jarmitage/Stenophone/teensyduino/stenophone/stenophone.h

#define TOTAL_CHANNELS 24
#define USED_CHANNELS 22

//============================================
//  Pin mappings
//============================================

// Breakout PCB Top Row 0-7
const int s160 = 12;
const int s161 = 11;
const int s162 = 10;
const int s163 = 9;
const int s80 = 8;
const int s81 = 7;
const int s82 = 6;

// Breakout PCB Bottom Row 0-7
const int com8 = 14;
const int en8 = 15;
const int com16 = 16;
const int en16 = 17;

const int led = 13; // Teensy Indicator LED
const int shiftKey = 5; // Microswitch
